ReadHegel/taipu/ergogen/output/outlines/xl_board_left.dxf

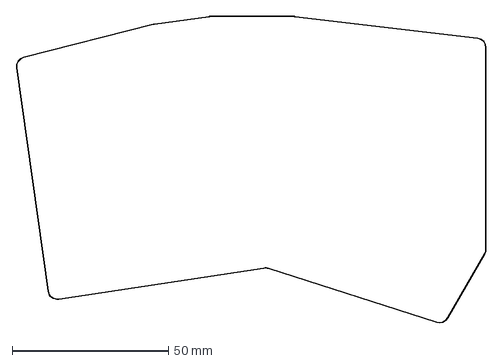
[picture p16: CAD file, 2025-08-07]
ergogen/output/outlines/xl_board_left.dxf
150.5 x 98.4 mm
