ReadHegel/taipu/ergogen/output/outlines/xl_board_right.dxf

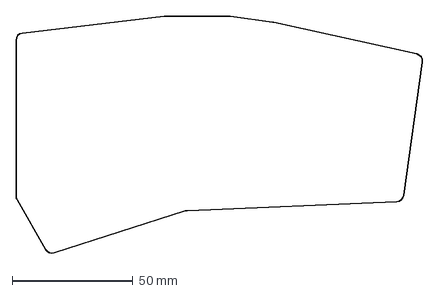
[picture p17: CAD file, 2025-08-07]
ergogen/output/outlines/xl_board_right.dxf
168.4 x 98.4 mm
