ReadHegel/taipu/ergogen/output/outlines/combo.dxf

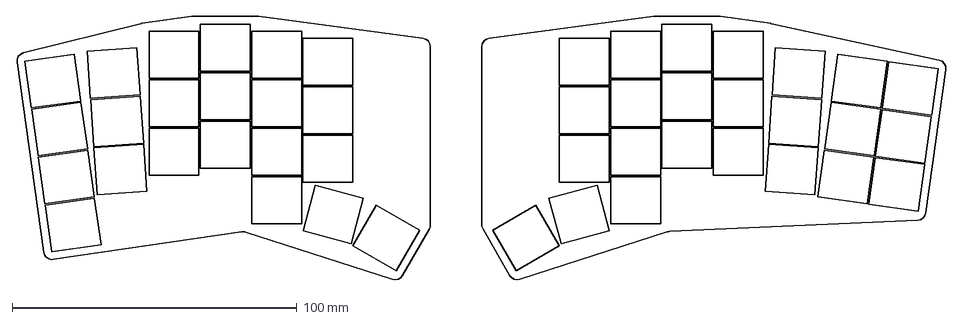
[picture p18: CAD file, 2025-07-15]
ergogen/output/outlines/combo.dxf
326.4 x 92.7 mm
