ReadHegel/taipu/ergogen/output/outlines/combo_right.dxf

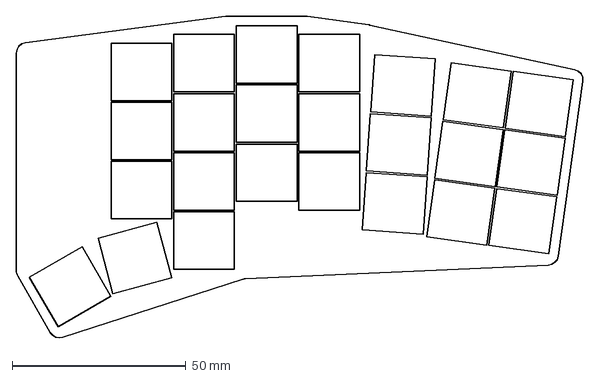
[picture p19: CAD file, 2025-07-15]
ergogen/output/outlines/combo_right.dxf
163.0 x 92.7 mm
