ReadHegel/taipu/ergogen/output/outlines/board_right.dxf

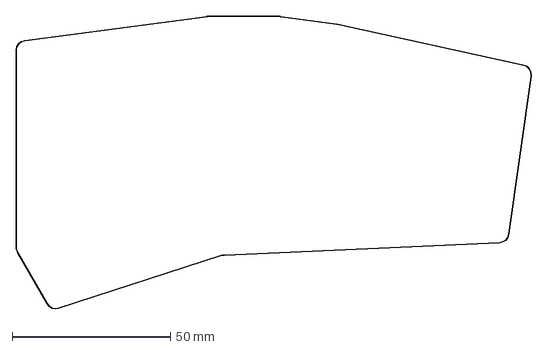
[picture p20: CAD file, 2025-07-15]
ergogen/output/outlines/board_right.dxf
163.0 x 92.7 mm
