ReadHegel/taipu/ergogen/output/outlines/raw.dxf

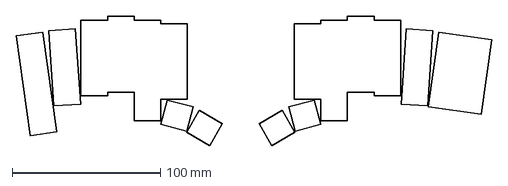
[picture p21: CAD file, 2025-07-15]
ergogen/output/outlines/raw.dxf
321.1 x 87.1 mm
