ReadHegel/taipu/ergogen/output/outlines/combo_left.dxf

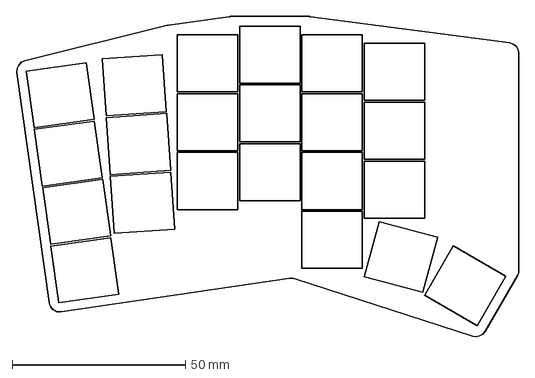
[picture p22: CAD file, 2025-07-15]
ergogen/output/outlines/combo_left.dxf
145.2 x 92.7 mm
