ReadHegel/taipu/ergogen/output/outlines/keys.dxf

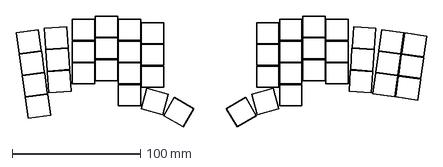
[picture p23: CAD file, 2025-07-15]
ergogen/output/outlines/keys.dxf
320.5 x 86.5 mm
