ReadHegel/taipu/ergogen/output/outlines/board_left.dxf

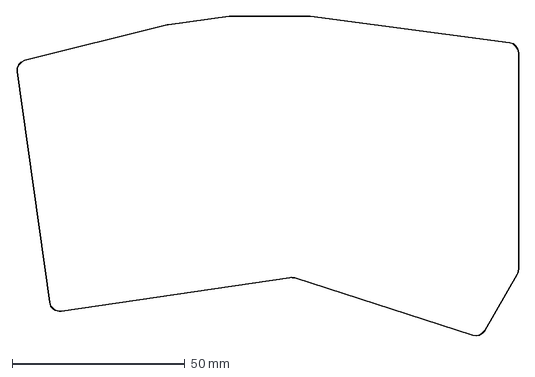
[picture p24: CAD file, 2025-07-15]
ergogen/output/outlines/board_left.dxf
145.2 x 92.7 mm
